createskyblue/PhotoelectricDoor/WINDOWS/img/2.png

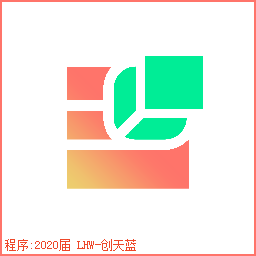
WINDOWS/img/2.png
