createskyblue/PhotoelectricDoor/WINDOWS/img/WorkMode.gif

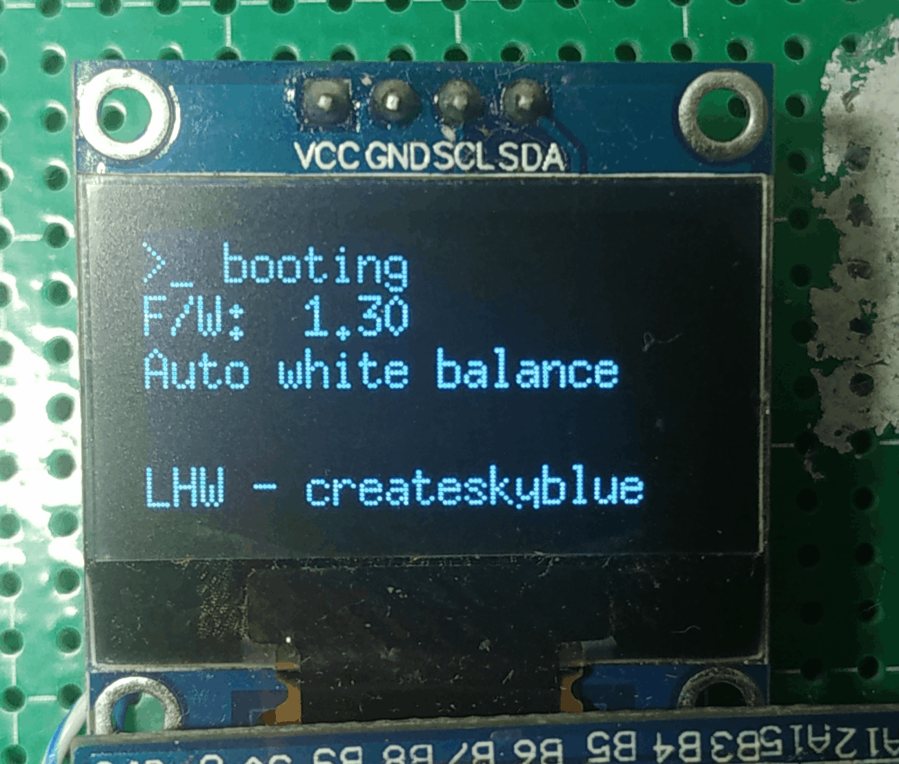
WINDOWS/img/WorkMode.gif
